lmartorella/net/schematics/opto.asc

C1: cap; 470n
D1: diode
I1: current; 100n
R1: res; 390k
R2: res; 390k
U1: 4N25
V1: voltage; SINE(0 325 50 0 0 0 25)
V2: voltage; 5
Named nets: 0, OUT
.tran 0 1 0 .001
;tran 1s startup step
